OLIMEX/AgonLight2/HARDWARE/AgonLight2_Rev_B/3d/TFC-WPAPR-08---112J-TXAR-R_C_1-1.STEP

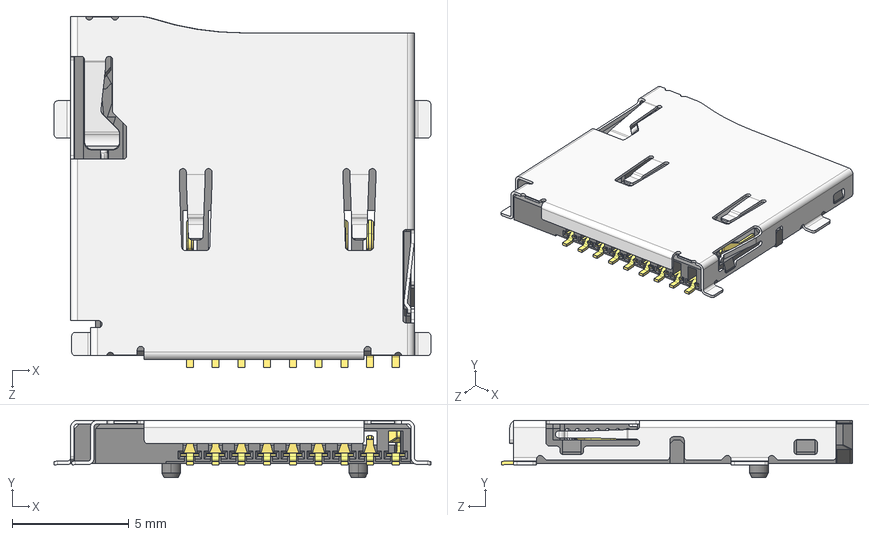
[picture p16: CAD file, 2023-07-12]
HARDWARE/AgonLight2_Rev_B/3d/TFC-WPAPR-08---112J-TXAR-R_C_1-1.STEP
16.1 x 2.45 x 15.0 mm
