OLIMEX/AgonLight2/HARDWARE/AgonLight2_Rev_B/3d/L-CD32_shielded.step

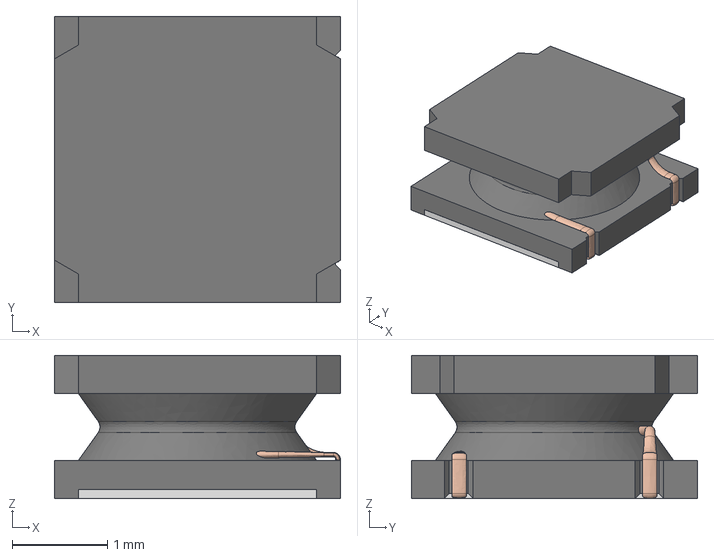
[picture p17: CAD file, 2023-07-12]
HARDWARE/AgonLight2_Rev_B/3d/L-CD32_shielded.step
3.00 x 3.00 x 1.50 mm
