OLIMEX/AgonLight2/HARDWARE/AgonLight2_Rev_B/3d/72w2538_292303-4.stp

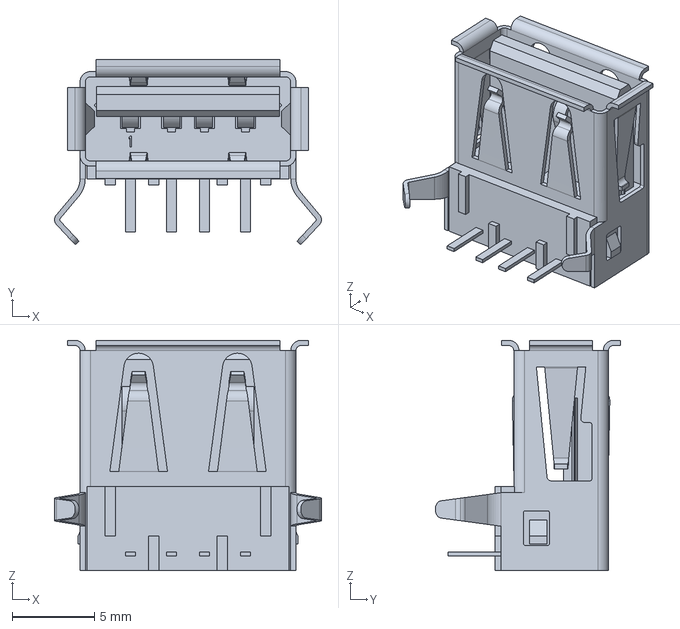
[picture p18: CAD file, 2023-07-12]
HARDWARE/AgonLight2_Rev_B/3d/72w2538_292303-4.stp
16.2 x 11.3 x 14.0 mm
