OLIMEX/AgonLight2/HARDWARE/AgonLight2_Rev_B/3d/DO-214AC_SMA.step

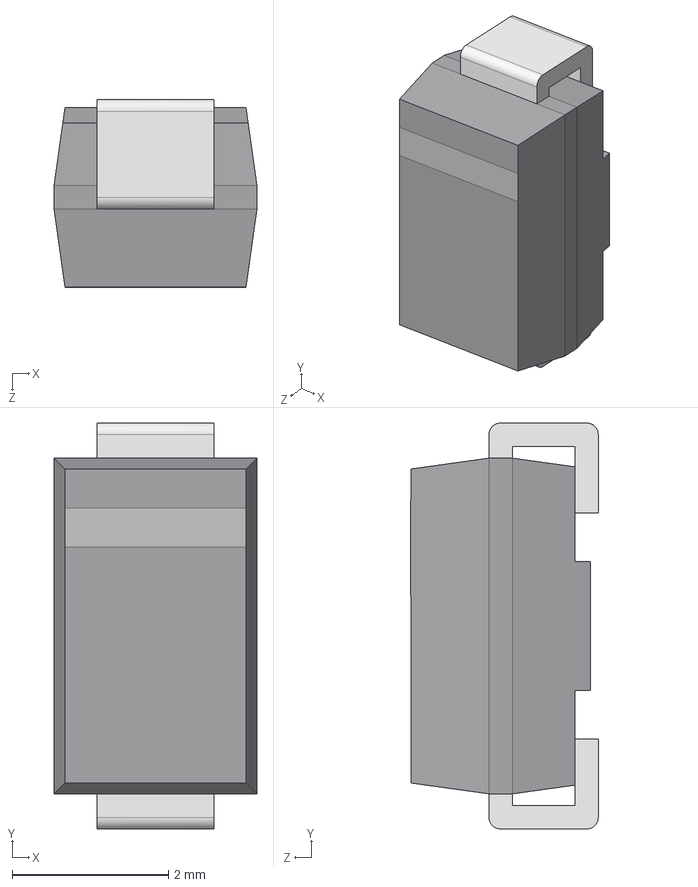
[picture p19: CAD file, 2023-07-12]
HARDWARE/AgonLight2_Rev_B/3d/DO-214AC_SMA.step
2.60 x 5.20 x 2.40 mm
