OLIMEX/AgonLight2/HARDWARE/AgonLight2_Rev_B/3d/Audio_Jack-3.5mm---CUI_SJ1-3515-SMT-TR.step

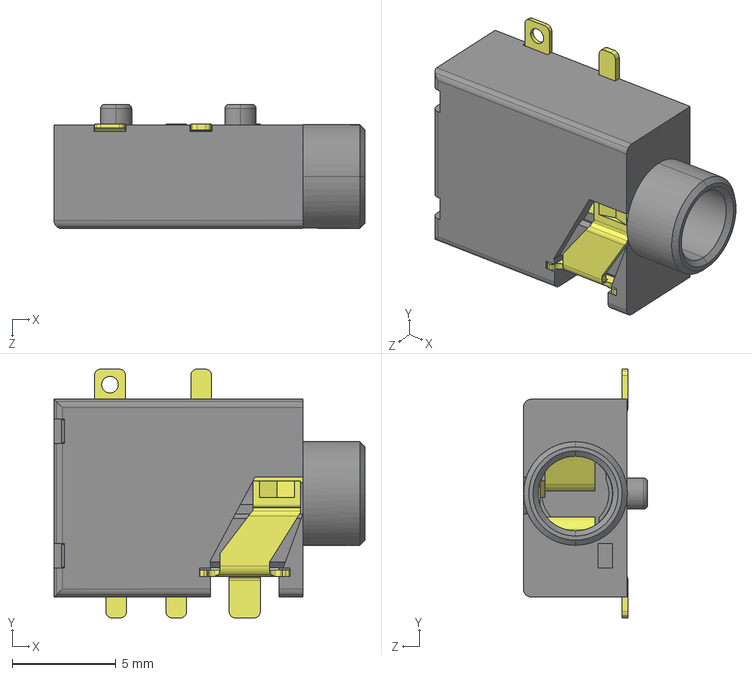
[picture p20: CAD file, 2023-07-12]
HARDWARE/AgonLight2_Rev_B/3d/Audio_Jack-3.5mm---CUI_SJ1-3515-SMT-TR.step
15.0 x 12.0 x 6.00 mm
