OLIMEX/AgonLight2/HARDWARE/AgonLight2_Rev_B/3d/JST_B2B-PH-SM4-TB(DW02R).step

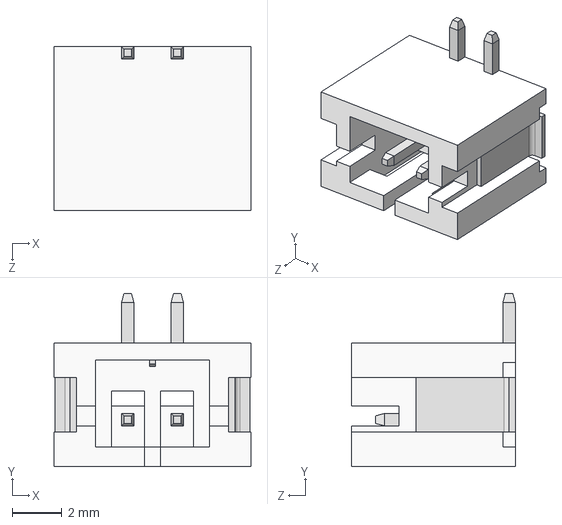
[picture p21: CAD file, 2023-07-12]
HARDWARE/AgonLight2_Rev_B/3d/JST_B2B-PH-SM4-TB(DW02R).step
7.95 x 7.00 x 6.60 mm
