OLIMEX/AgonLight2/HARDWARE/AgonLight2_Rev_B/3d/User Library-SOT50P160X60-6.step

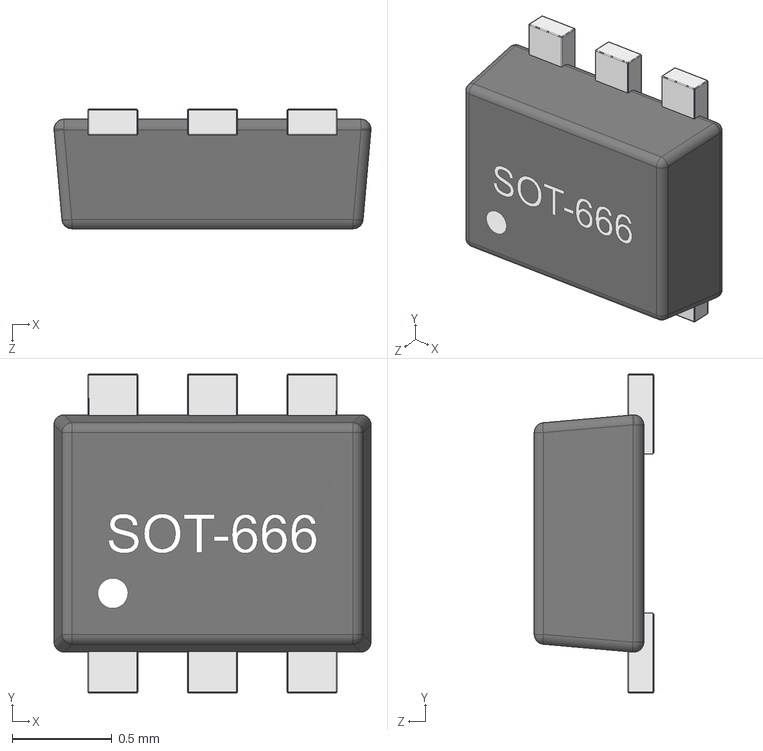
[picture p22: CAD file, 2023-07-12]
HARDWARE/AgonLight2_Rev_B/3d/User Library-SOT50P160X60-6.step
1.59 x 1.60 x 0.6 mm
