OLIMEX/AgonLight2/HARDWARE/AgonLight2_Rev_B/3d/SOT-23-6.step

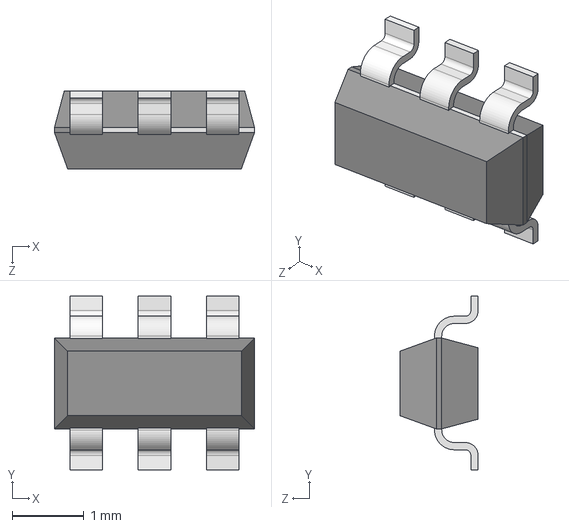
[picture p23: CAD file, 2023-07-12]
HARDWARE/AgonLight2_Rev_B/3d/SOT-23-6.step
2.79 x 2.43 x 1.09 mm
