OLIMEX/AgonLight2/HARDWARE/AgonLight2_Rev_B/3d/HN1x4-PinHeader_1x04_P2.54mm_Vertical.step

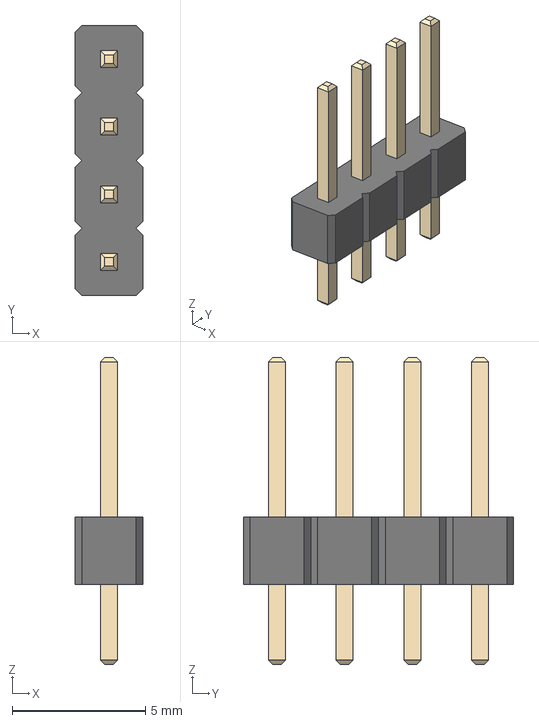
[picture p24: CAD file, 2022-12-14]
HARDWARE/AgonLight2_Rev_B/3d/HN1x4-PinHeader_1x04_P2.54mm_Vertical.step
2.54 x 10.2 x 11.5 mm
