OLIMEX/AgonLight2/HARDWARE/AgonLight2_Rev_B/3d/HN1x2-PinHeader_1x02_P2.54mm_Vertical.step

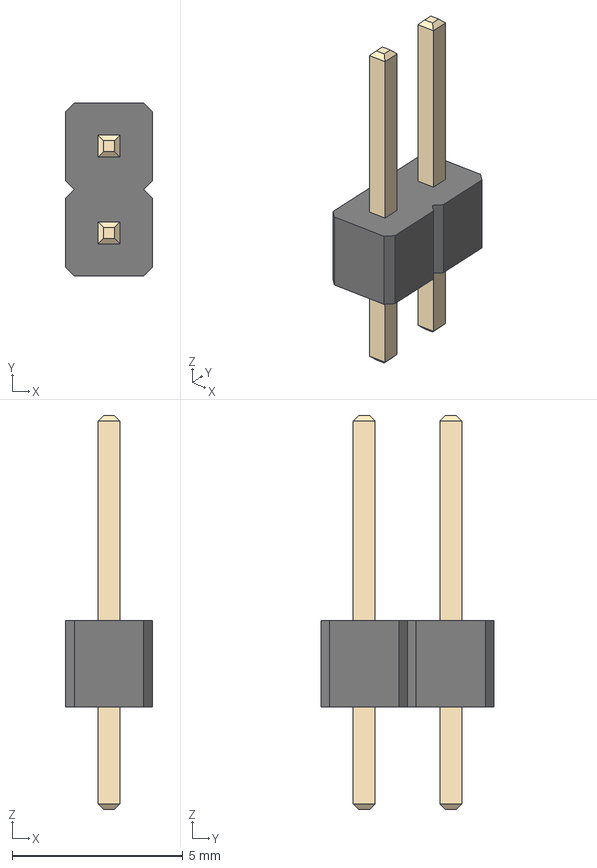
[picture p25: CAD file, 2022-12-14]
HARDWARE/AgonLight2_Rev_B/3d/HN1x2-PinHeader_1x02_P2.54mm_Vertical.step
2.54 x 5.08 x 11.5 mm
