OLIMEX/AgonLight2/SOFTWARE/4-AgonLight2-Console8/basic_examples_tests/olimex_challenge/ISSUE-3/SOLUTION-6/snakedemake.png

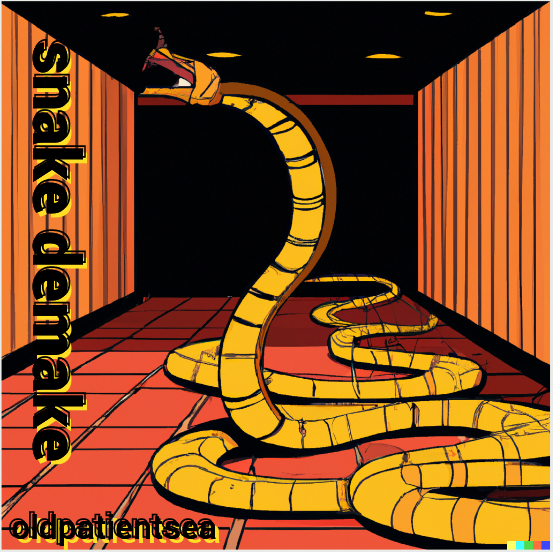
SOFTWARE/4-AgonLight2-Console8/basic_examples_tests/olimex_challenge/ISSUE-3/SOLUTION-6/snakedemake.png
