OLIMEX/AgonLight2/SOFTWARE/2-AgonLight2-VDP-104/source/video/agon_fonts.h

//
// Title:			Agon Video BIOS - font file
// Author:			Damien Guard
//					Lennart Benschop
// Created:			06/08/2022
// Last Updated:	20/02/2023
//
// Modinfo:
// 17/08/2022:		Implemented Acorn font
// 05/09/2022:		Renamed file
// 20/02/2023:		Marked out non-standard CP-1252 characters in comments, fixed £ and `
// 14/10/2023:		LB: Added CP1252 characters from BBC Basic for SDL2, kept all Agon ASCII characters as is, including £
//
// BBC Basic for SDL2 is
// Copyright (c) 2021, Richard T. Russell, http://www.rtrussell.co.uk/
// 
// This software is provided 'as-is', without any express or implied
// warranty.  In no event will the authors be held liable for any damages
// arising from the use of this software.

// Permission is granted to anyone to use this software for any purpose,
// including commercial applications, and to alter it and redistribute it
// freely, subject to the following restrictions:

// 1. The origin of this software must not be misrepresented; you must not
//    claim that you wrote the original software.  If you use this software
//    in a product, an acknowledgment in the product documentation would be
//    appreciated but is not required.

// 2. Altered source versions must be plainly marked as such, and must not be
//    misrepresented as being the original software.

// 3. This notice may not be removed or altered from any source distribution.

#pragma once

namespace fabgl {

	uint8_t FONT_AGON_DATA[256*8]; 

	static const uint8_t FONT_AGON_BITMAP[] = {
		0x00, 0x00, 0x00, 0x00, 0x00, 0x00, 0x00, 0x00, //  
		0x18, 0x18, 0x18, 0x18, 0x18, 0x00, 0x18, 0x00, // !
		0x6c, 0x6c, 0x6c, 0x00, 0x00, 0x00, 0x00, 0x00, // "
		0x36, 0x36, 0x7f, 0x36, 0x7f, 0x36, 0x36, 0x00, // #
		0x0c, 0x3f, 0x68, 0x3e, 0x0b, 0x7e, 0x18, 0x00, // $
		0x60, 0x66, 0x0c, 0x18, 0x30, 0x66, 0x06, 0x00, // %
		0x38, 0x6c, 0x6c, 0x38, 0x6d, 0x66, 0x3b, 0x00, // &
		0x0c, 0x18, 0x30, 0x00, 0x00, 0x00, 0x00, 0x00, // '
		0x0c, 0x18, 0x30, 0x30, 0x30, 0x18, 0x0c, 0x00, // (
		0x30, 0x18, 0x0c, 0x0c, 0x0c, 0x18, 0x30, 0x00, // )
		0x00, 0x18, 0x7e, 0x3c, 0x7e, 0x18, 0x00, 0x00, // *
		0x00, 0x18, 0x18, 0x7e, 0x18, 0x18, 0x00, 0x00, // +
		0x00, 0x00, 0x00, 0x00, 0x00, 0x18, 0x18, 0x30, // ,
		0x00, 0x00, 0x00, 0x7e, 0x00, 0x00, 0x00, 0x00, // -
		0x00, 0x00, 0x00, 0x00, 0x00, 0x18, 0x18, 0x00, // .
		0x00, 0x06, 0x0c, 0x18, 0x30, 0x60, 0x00, 0x00, // /

		0x3c, 0x66, 0x6e, 0x7e, 0x76, 0x66, 0x3c, 0x00, // 0
		0x18, 0x38, 0x18, 0x18, 0x18, 0x18, 0x7e, 0x00, // 1
		0x3c, 0x66, 0x06, 0x0c, 0x18, 0x30, 0x7e, 0x00, // 2
		0x3c, 0x66, 0x06, 0x1c, 0x06, 0x66, 0x3c, 0x00, // 3
		0x0c, 0x1c, 0x3c, 0x6c, 0x7e, 0x0c, 0x0c, 0x00, // 4
		0x7e, 0x60, 0x7c, 0x06, 0x06, 0x66, 0x3c, 0x00, // 5
		0x1c, 0x30, 0x60, 0x7c, 0x66, 0x66, 0x3c, 0x00, // 6
		0x7e, 0x06, 0x0c, 0x18, 0x30, 0x30, 0x30, 0x00, // 7
		0x3c, 0x66, 0x66, 0x3c, 0x66, 0x66, 0x3c, 0x00, // 8
		0x3c, 0x66, 0x66, 0x3e, 0x06, 0x0c, 0x38, 0x00, // 9
		0x00, 0x00, 0x18, 0x18, 0x00, 0x18, 0x18, 0x00, // :
		0x00, 0x00, 0x18, 0x18, 0x00, 0x18, 0x18, 0x30, // ;
		0x0c, 0x18, 0x30, 0x60, 0x30, 0x18, 0x0c, 0x00, // <
		0x00, 0x00, 0x7e, 0x00, 0x7e, 0x00, 0x00, 0x00, // =
		0x30, 0x18, 0x0c, 0x06, 0x0c, 0x18, 0x30, 0x00, // >
		0x3c, 0x66, 0x0c, 0x18, 0x18, 0x00, 0x18, 0x00, // ?

		0x3c, 0x66, 0x6e, 0x6a, 0x6e, 0x60, 0x3c, 0x00, // @
		0x3c, 0x66, 0x66, 0x7e, 0x66, 0x66, 0x66, 0x00, // A
		0x7c, 0x66, 0x66, 0x7c, 0x66, 0x66, 0x7c, 0x00, // B
		0x3c, 0x66, 0x60, 0x60, 0x60, 0x66, 0x3c, 0x00, // C
		0x78, 0x6c, 0x66, 0x66, 0x66, 0x6c, 0x78, 0x00, // D
		0x7e, 0x60, 0x60, 0x7c, 0x60, 0x60, 0x7e, 0x00, // E
		0x7e, 0x60, 0x60, 0x7c, 0x60, 0x60, 0x60, 0x00, // F
		0x3c, 0x66, 0x60, 0x6e, 0x66, 0x66, 0x3c, 0x00, // G
		0x66, 0x66, 0x66, 0x7e, 0x66, 0x66, 0x66, 0x00, // H
		0x7e, 0x18, 0x18, 0x18, 0x18, 0x18, 0x7e, 0x00, // I
		0x3e, 0x0c, 0x0c, 0x0c, 0x0c, 0x6c, 0x38, 0x00, // J
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
	};

	extern const FontInfo FONT_AGON = {
		.pointSize = 6,
		.width     = 8,
		.height    = 8,
		.ascent    = 7,
		.inleading = 0,
		.exleading = 0,
		.flags     = 0,
		.weight    = 400,
		.charset   = 255,
		.data      = FONT_AGON_DATA,
		.chptr     = nullptr,
		.codepage  = 1252,
	};
}
