OLIMEX/AgonLight2/SOFTWARE/2-AgonLight2-VDP-104/source/video/graphics.h

#ifndef GRAPHICS_H
#define GRAPHICS_H

#include <fabgl.h>

#include "agon.h"
#include "agon_ps2.h"
#include "agon_screen.h"
#include "agon_fonts.h"							// The Acorn BBC Micro Font
#include "agon_palette.h"						// Colour lookup table
#include "cursor.h"
#include "sprites.h"
#include "viewport.h"

fabgl::PaintOptions			gpo;				// Graphics paint options
fabgl::PaintOptions			tpo;				// Text paint options

Point			p1, p2, p3;						// Coordinate store for plot
Point			rp1, rp2, rp3;					// Relative coordinates store for plot
RGB888			gfg, gbg;						// Graphics foreground and background colour
RGB888			tfg, tbg;						// Text foreground and background colour
uint8_t			fontW;							// Font width
uint8_t			fontH;							// Font height
uint8_t			videoMode;						// Current video mode
bool			legacyModes = false;			// Default legacy modes being false
bool			rectangularPixels = false;		// Pixels are square by default
uint8_t			palette[64];					// Storage for the palette


// Copy the AGON font data from Flash to RAM
//
void copy_font() {
	memcpy(fabgl::FONT_AGON_DATA + 256, fabgl::FONT_AGON_BITMAP, sizeof(fabgl::FONT_AGON_BITMAP));
}

// Redefine a character in the font
//
void redefineCharacter(uint8_t c, uint8_t * data) {
	memcpy(&fabgl::FONT_AGON_DATA[c * 8], data, 8);
}

bool cmpChar(uint8_t * c1, uint8_t *c2, uint8_t len) {
	for (uint8_t i = 0; i < len; i++) {
		if (*c1++ != *c2++) {
			return false;
		}
	}
	return true;
}

// Try and match a character at given pixel position
//
char getScreenChar(uint16_t px, uint16_t py) {
	RGB888	pixel;
	uint8_t	charRow;
	uint8_t	charData[8];
	uint8_t R = tbg.R;
	uint8_t G = tbg.G;
	uint8_t B = tbg.B;

	// Do some bounds checking first
	//
	if (px >= canvasW - 8 || py >= canvasH - 8) {
		return 0;
	}
	if (ttxtMode) {
		return ttxt_instance.get_screen_char(px,py);
	} else {
		// Now scan the screen and get the 8 byte pixel representation in charData
		//
		for (uint8_t y = 0; y < 8; y++) {
	    	charRow = 0;
	    	for (uint8_t x = 0; x < 8; x++) {
	      		pixel = canvas->getPixel(px + x, py + y);
	      		if (!(pixel.R == R && pixel.G == G && pixel.B == B)) {
					charRow |= (0x80 >> x);
	    		}
	    	}
	    	charData[y] = charRow;
		}
		//
		// Finally try and match with the character set array
		//
		for (auto i = 32; i <= 255; i++) {
	    	if (cmpChar(charData, &fabgl::FONT_AGON_DATA[i * 8], 8)) {	
	    		return i;		
			}
		}
	}
	return 0;
}

// Get pixel value at screen coordinates
//
RGB888 getPixel(uint16_t x, uint16_t y) {
	Point p = translateCanvas(scale(x, y));
	if (p.X >= 0 && p.Y >= 0 && p.X < canvasW && p.Y < canvasH) {
		return canvas->getPixel(p.X, p.Y);
	}
	return RGB888(0,0,0);
}

// Get the palette index for a given RGB888 colour
//
uint8_t getPaletteIndex(RGB888 colour) {
	for (uint8_t i = 0; i < getVGAColourDepth(); i++) {
		if (colourLookup[palette[i]] == colour) {
			return i;
		}
	}
	return 0;
}

// Set logical palette
// Parameters:
// - l: The logical colour to change
// - p: The physical colour to change
// - r: The red component
// - g: The green component
// - b: The blue component
//
void setPalette(uint8_t l, uint8_t p, uint8_t r, uint8_t g, uint8_t b) {
	RGB888 col;				// The colour to set

	if (getVGAColourDepth() < 64) {		// If it is a paletted video mode
		if (p == 255) {					// If p = 255, then use the RGB values
			col = RGB888(r, g, b);
		} else if (p < 64) {			// If p < 64, then look the value up in the colour lookup table
			col = colourLookup[p];
		} else {				
			debug_log("vdu_palette: p=%d not supported\n\r", p);
			return;
		}
		setPaletteItem(l, col);
		debug_log("vdu_palette: %d,%d,%d,%d,%d\n\r", l, p, r, g, b);
	} else {
		debug_log("vdu_palette: not supported in this mode\n\r");
	}
}

// Reset the palette and set the foreground and background drawing colours
// Parameters:
// - colour: Array of indexes into colourLookup table
// - sizeOfArray: Size of passed colours array
//
void resetPalette(const uint8_t colours[]) {
	if (ttxtMode) return;
	for (uint8_t i = 0; i < 64; i++) {
		uint8_t c = colours[i % getVGAColourDepth()];
		palette[i] = c;
		setPaletteItem(i, colourLookup[c]);
	}
	updateRGB2PaletteLUT();
}

// Get the paint options for a given GCOL mode
//
fabgl::PaintOptions getPaintOptions(uint8_t mode, fabgl::PaintOptions priorPaintOptions) {
	fabgl::PaintOptions p = priorPaintOptions;
	
	switch (mode) {
		case 0: p.NOT = 0; p.swapFGBG = 0; break;
		case 4: p.NOT = 1; p.swapFGBG = 0; break;
	}
	return p;
}

// Set text colour (handles COLOUR / VDU 17)
//
void setTextColour(uint8_t colour) {
	if (ttxtMode) return;

	uint8_t c = palette[colour % getVGAColourDepth()];

	if (colour < 64) {
		tfg = colourLookup[c];
		debug_log("vdu_colour: tfg %d = %02X : %02X,%02X,%02X\n\r", colour, c, tfg.R, tfg.G, tfg.B);
	}
	else if (colour >= 128 && colour < 192) {
		tbg = colourLookup[c];
		debug_log("vdu_colour: tbg %d = %02X : %02X,%02X,%02X\n\r", colour, c, tbg.R, tbg.G, tbg.B);	
	}
	else {
		debug_log("vdu_colour: invalid colour %d\n\r", colour);
	}
}

// Set graphics colour (handles GCOL / VDU 18)
//
void setGraphicsColour(uint8_t mode, uint8_t colour) {
	if (ttxtMode) return;
	
	uint8_t c = palette[colour % getVGAColourDepth()];

	if (mode <= 6) {
		if (colour < 64) {
			gfg = colourLookup[c];
			debug_log("vdu_gcol: mode %d, gfg %d = %02X : %02X,%02X,%02X\n\r", mode, colour, c, gfg.R, gfg.G, gfg.B);
		}
		else if (colour >= 128 && colour < 192) {
			gbg = colourLookup[c];
			debug_log("vdu_gcol: mode %d, gbg %d = %02X : %02X,%02X,%02X\n\r", mode, colour, c, gbg.R, gbg.G, gbg.B);
		}
		else {
			debug_log("vdu_gcol: invalid colour %d\n\r", colour);
		}
		gpo = getPaintOptions(mode, gpo);
	}
	else {
		debug_log("vdu_gcol: invalid mode %d\n\r", mode);
	}
}

// Clear a viewport
//
void clearViewport(Rect * viewport) {
	if (ttxtMode) {
		ttxt_instance.cls();
	} else {       
  		if (canvas) {
	  		if (useViewports) {
		  		canvas->fillRectangle(*viewport);
		  	}
		  	else {
			  canvas->clear();
			}
	  	}
	}
}

//// Graphics drawing routines

// Push point to list
//
void pushPoint(Point p) {
	rp3 = rp2;
	rp2 = rp1;
	rp1 = Point(p.X - p1.X, p.Y - p1.Y);
	p3 = p2;
	p2 = p1;
	p1 = p;
}
void pushPoint(uint16_t x, uint16_t y) {
	pushPoint(translateCanvas(scale(x, y)));
}
void pushPointRelative(int16_t x, int16_t y) {
	auto scaledPoint = scale(x, y);
	pushPoint(Point(p1.X + scaledPoint.X, p1.Y + (logicalCoords ? -scaledPoint.Y : scaledPoint.Y)));
}

// get graphics cursor
//
Point * getGraphicsCursor() {
	return &p1;
}

// Set up canvas for drawing graphics
//
void setGraphicsOptions(uint8_t mode) {
	auto colourMode = mode & 0x03;
	canvas->setClippingRect(graphicsViewport);
	switch (colourMode) {
		case 0: break;	// move command
		case 1: {
			// use fg colour
			canvas->setPenColor(gfg);
		} break;
		case 2: break;	// logical inverse colour (not suported)
		case 3: {
			// use bg colour
			canvas->setPenColor(gbg);
		} break;
	}
	canvas->setPaintOptions(gpo);
}

// Set up canvas for drawing filled graphics
//
void setGraphicsFill(uint8_t mode) {
	auto colourMode = mode & 0x03;
	switch (colourMode) {
		case 0: break;	// move command
		case 1: {
			// use fg colour
			canvas->setBrushColor(gfg);
		} break;
		case 2: break;	// logical inverse colour (not suported)
		case 3: {
			// use bg colour
			canvas->setBrushColor(gbg);
		} break;
	}
}

// Move to
//
void moveTo() {
	canvas->moveTo(p1.X, p1.Y);
}

// Line plot
//
void plotLine(bool omitFirstPoint = false, bool omitLastPoint = false) {
	RGB888 firstPixelColour;
	RGB888 lastPixelColour;
	if (omitFirstPoint) {
		firstPixelColour = canvas->getPixel(p2.X, p2.Y);
	}
	if (omitLastPoint) {
		lastPixelColour = canvas->getPixel(p1.X, p1.Y);
	}
	canvas->lineTo(p1.X, p1.Y);
	if (omitFirstPoint) {
		canvas->setPixel(p2, firstPixelColour);
	}
	if (omitLastPoint) {
		canvas->setPixel(p1, lastPixelColour);
	}
}

// Point point
//
void plotPoint() {
	canvas->setPixel(p1.X, p1.Y);
}

// Triangle plot
//
void plotTriangle() {
	Point p[3] = {
		p3,
		p2,
		p1, 
	};
	canvas->drawPath(p, 3);
	canvas->fillPath(p, 3);
}

// Rectangle plot
//
void plotRectangle() {
	canvas->fillRectangle(p2.X, p2.Y, p1.X, p1.Y);
}

// Parallelogram plot
//
void plotParallelogram() {
	Point p[4] = {
		p3,
		p2,
		p1,
		Point(p1.X + (p3.X - p2.X), p1.Y + (p3.Y - p2.Y)),
	};
	canvas->drawPath(p, 4);
	canvas->fillPath(p, 4);
}

// Circle plot
//
void plotCircle(bool filled = false) {
	auto size = 2 * sqrt(rp1.X * rp1.X + (rp1.Y * rp1.Y * (rectangularPixels ? 4 : 1)));
	if (filled) {
		canvas->fillEllipse(p2.X, p2.Y, size, rectangularPixels ? size / 2 : size);
	} else {
		canvas->drawEllipse(p2.X, p2.Y, size, rectangularPixels ? size / 2 : size);
	}
}

// Copy or move a rectangle
//
void plotCopyMove(uint8_t mode) {
	uint16_t x = p1.X;
	uint16_t y = p1.Y;
	uint16_t width = abs(p3.X - p2.X) + 1;
	uint16_t height = abs(p3.Y - p2.Y) + 1;
	uint16_t sourceX = p3.X < p2.X ? p3.X : p2.X;
	uint16_t sourceY = p3.Y < p2.Y ? p3.Y : p2.Y;

	debug_log("plotCopyMove: mode %d, (%d,%d) -> (%d,%d), width: %d, height: %d\n\r", mode, sourceX, sourceY, x, y, width, height);
	canvas->copyRect(sourceX, sourceY, x, y - height, width, height);
	if (mode == 1 || mode == 5) {
		// move rectangle needs to clear source rectangle
		// being careful not to clear the destination rectangle
		canvas->setBrushColor(gbg);
		Rect sourceRect = Rect(sourceX, sourceY, sourceX + width, sourceY + height);
		Rect destRect = Rect(x, y - height, x + width, y);
		if (sourceRect.intersects(destRect)) {
			// we can use clipping rects to block out parts of the screen
			// the areas above, below, left, and right of the destination rectangle
			// and then draw rectangles over our source rectangle
			auto intersection = sourceRect.intersection(destRect);

			if (intersection.X1 > sourceRect.X1) {
				// fill in source area to the left of destination
				debug_log("clearing left of destination\n\r");
				canvas->setClippingRect(Rect(sourceRect.X1, sourceRect.Y1, intersection.X1 - 1, sourceRect.Y2));
				canvas->fillRectangle(sourceRect);
			}
			if (intersection.X2 < sourceRect.X2) {
				// fill in source area to the right of destination
				debug_log("clearing right of destination\n\r");
				canvas->setClippingRect(Rect(intersection.X2, sourceRect.Y1, sourceRect.X2, sourceRect.Y2));
				canvas->fillRectangle(sourceRect);
			}
			if (intersection.Y1 > sourceRect.Y1) {
				// fill in source area above destination
				debug_log("clearing above destination\n\r");
				canvas->setClippingRect(Rect(sourceRect.X1, sourceRect.Y1, sourceRect.X2, intersection.Y1 - 1));
				canvas->fillRectangle(sourceRect);
			}
			if (intersection.Y2 < sourceRect.Y2) {
				// fill in source area below destination
				debug_log("clearing below destination\n\r");
				canvas->setClippingRect(Rect(sourceRect.X1, intersection.Y2, sourceRect.X2, sourceRect.Y2));
				canvas->fillRectangle(sourceRect);
			}
		} else {
			canvas->fillRectangle(sourceRect);
		}
	}
}

// Plot bitmap
//
void plotBitmap() {
	drawBitmap(p1.X, p1.Y);
}

// Character plot
//
void plotCharacter(char c) {
	if (ttxtMode) {
    	ttxt_instance.draw_char(activeCursor->X, activeCursor->Y, c);
  	} else {
  		if (textCursorActive()) {
	  		canvas->setClippingRect(defaultViewport);
			canvas->setPenColor(tfg);
			canvas->setBrushColor(tbg);
			canvas->setPaintOptions(tpo);
	  	} else {
		  canvas->setClippingRect(graphicsViewport);
		  canvas->setPenColor(gfg);
		  canvas->setPaintOptions(gpo);
		}
		canvas->drawChar(activeCursor->X, activeCursor->Y, c);
  	}
	cursorRight();
}

// Backspace plot
//
void plotBackspace() {
	cursorLeft();
	if (ttxtMode) {
		ttxt_instance.draw_char(activeCursor->X, activeCursor->Y, ' ');
	} else {
		canvas->setBrushColor(textCursorActive() ? tbg : gbg);
		canvas->fillRectangle(activeCursor->X, activeCursor->Y, activeCursor->X + fontW - 1, activeCursor->Y + fontH - 1);
	}
}

// Set character overwrite mode (background fill)
//
inline void setCharacterOverwrite(bool overwrite) {
	canvas->setGlyphOptions(GlyphOptions().FillBackground(overwrite));
}

// Set a clipping rectangle
//
void setClippingRect(Rect rect) {
	canvas->setClippingRect(rect);
}

// Draw cursor
//
void drawCursor(Point p) {
	canvas->swapRectangle(p.X, p.Y, p.X + fontW - 1, p.Y + fontH - 1);
}


// Clear the screen
// 
void cls(bool resetViewports) {
	if (resetViewports) {
    	if (ttxtMode) {
    		ttxt_instance.set_window(0,24,39,0);
		}
		viewportReset();
	}
	if (canvas) {
		canvas->setPenColor(tfg);
		canvas->setBrushColor(tbg);	
		canvas->setPaintOptions(tpo);
		clearViewport(getViewport(VIEWPORT_TEXT));
	}
	if (hasActiveSprites()) {
		activateSprites(0);
		clearViewport(getViewport(VIEWPORT_TEXT));
	}
	homeCursor();
	setPagedMode();
}

// Clear the graphics area
//
void clg() {
	if (canvas) {
		canvas->setPenColor(gfg);
		canvas->setBrushColor(gbg);	
		canvas->setPaintOptions(gpo);
		clearViewport(getViewport(VIEWPORT_GRAPHICS));
	}
	pushPoint(0, 0);		// Reset graphics origin (as per BBC Micro CLG)
}

// Do the mode change
// Parameters:
// - mode: The video mode
// Returns:
// -  0: Successful
// -  1: Invalid # of colours
// -  2: Not enough memory for mode
// - -1: Invalid mode
//
int8_t change_mode(uint8_t mode) {
	int8_t errVal = -1;

	cls(true);
	ttxtMode = false;
	switch (mode) {
		case 0:
			if (legacyModes == true) {
				errVal = change_resolution(2, SVGA_1024x768_60Hz);
			} else {
				errVal = change_resolution(16, VGA_640x480_60Hz);	// VDP 1.03 Mode 3, VGA Mode 12h
			}
			break;
		case 1:
			if (legacyModes == true) {
				errVal = change_resolution(16, VGA_512x384_60Hz);
			} else {
				errVal = change_resolution(4, VGA_640x480_60Hz);
			}
			break;
		case 2:
			if (legacyModes == true) {
				errVal = change_resolution(64, VGA_320x200_75Hz);
			} else {
				errVal = change_resolution(2, VGA_640x480_60Hz);
			}
			break;
		case 3:
			if (legacyModes == true) {
				errVal = change_resolution(16, VGA_640x480_60Hz);
			} else {
				errVal = change_resolution(64, VGA_640x240_60Hz);
			}
			break;
		case 4:
			errVal = change_resolution(16, VGA_640x240_60Hz);
			break;
		case 5:
			errVal = change_resolution(4, VGA_640x240_60Hz);
			break;
		case 6:
			errVal = change_resolution(2, VGA_640x240_60Hz);
			break;
		case 7:
	    	errVal = change_resolution(16, VGA_640x480_60Hz);
	    	if (errVal == 0) {
	      		errVal = ttxt_instance.init();
	    		if (errVal == 0) ttxtMode = true; 
	    	}
	    	break;
		case 8:
			errVal = change_resolution(64, QVGA_320x240_60Hz);		// VGA "Mode X"
			break;
		case 9:
			errVal = change_resolution(16, QVGA_320x240_60Hz);
			break;
		case 10:
			errVal = change_resolution(4, QVGA_320x240_60Hz);
			break;
		case 11:
			errVal = change_resolution(2, QVGA_320x240_60Hz);
			break;
		case 12:
			errVal = change_resolution(64, VGA_320x200_70Hz);		// VGA Mode 13h
			break;
		case 13:
			errVal = change_resolution(16, VGA_320x200_70Hz);
			break;
		case 14:
			errVal = change_resolution(4, VGA_320x200_70Hz);
			break;
		case 15:
			errVal = change_resolution(2, VGA_320x200_70Hz);
			break;
		case 16:
			errVal = change_resolution(4, SVGA_800x600_60Hz);
			break;
		case 17:
			errVal = change_resolution(2, SVGA_800x600_60Hz);
			break;
		case 18:
			errVal = change_resolution(2, SVGA_1024x768_60Hz);		// VDP 1.03 Mode 0
			break;
		case 129:
			errVal = change_resolution(4, VGA_640x480_60Hz, true);
			break;
		case 130:
			errVal = change_resolution(2, VGA_640x480_60Hz, true);
			break;
		case 132:
			errVal = change_resolution(16, VGA_640x240_60Hz, true);
			break;
		case 133:
			errVal = change_resolution(4, VGA_640x240_60Hz, true);
			break;
		case 134:
			errVal = change_resolution(2, VGA_640x240_60Hz, true);
			break;
		case 136:
			errVal = change_resolution(64, QVGA_320x240_60Hz, true);		// VGA "Mode X"
			break;
		case 137:
			errVal = change_resolution(16, QVGA_320x240_60Hz, true);
			break;
		case 138:
			errVal = change_resolution(4, QVGA_320x240_60Hz, true);
			break;	
		case 139:
			errVal = change_resolution(2, QVGA_320x240_60Hz, true);
			break;
		case 140:
			errVal = change_resolution(64, VGA_320x200_70Hz, true);		// VGA Mode 13h
			break;
		case 141:
			errVal = change_resolution(16, VGA_320x200_70Hz, true);
			break;
		case 142:
			errVal = change_resolution(4, VGA_320x200_70Hz, true);
			break;
		case 143:
			errVal = change_resolution(2, VGA_320x200_70Hz, true);
			break;									
	}
	if (errVal != 0) {
		return errVal;
	}
	switch (getVGAColourDepth()) {
		case  2: resetPalette(defaultPalette02); break;
		case  4: resetPalette(defaultPalette04); break;
		case  8: resetPalette(defaultPalette08); break;
		case 16: resetPalette(defaultPalette10); break;
		case 64: resetPalette(defaultPalette40); break;
	}
	tpo = getPaintOptions(0, tpo);
	gpo = getPaintOptions(0, gpo);
	gfg = colourLookup[0x3F];
	gbg = colourLookup[0x00];
	tfg = colourLookup[0x3F];
	tbg = colourLookup[0x00];
	if (!ttxtMode) {
		canvas->selectFont(&fabgl::FONT_AGON);
	}
	setCharacterOverwrite(true);
	canvas->setPenWidth(1);
	setCanvasWH(canvas->getWidth(), canvas->getHeight());
	// simple heuristic to determine rectangular pixels
	rectangularPixels = ((float)canvasW / (float)canvasH) > 2;
	fontW = canvas->getFontInfo()->width;
	fontH = canvas->getFontInfo()->height;
	viewportReset();
	setOrigin(0,0);
	pushPoint(0,0);
	pushPoint(0,0);
	pushPoint(0,0);
	moveTo();
	resetCursor();
	homeCursor();
	if (isDoubleBuffered()) {
		switchBuffer();
		cls(false);
	}
	resetMousePositioner(canvasW, canvasH, _VGAController.get());
	setMouseCursor();
	debug_log("do_modeChange: canvas(%d,%d), scale(%f,%f), mode %d, videoMode %d\n\r", canvasW, canvasH, logicalScaleX, logicalScaleY, mode, videoMode);
	return 0;
}

// Change the video mode
// If there is an error, restore the last mode
// Parameters:
// - mode: The video mode
//
void set_mode(uint8_t mode) {
	auto errVal = change_mode(mode);
	if (errVal != 0) {
		debug_log("set_mode: error %d\n\r", errVal);
		errVal = change_mode(videoMode);
		if (errVal != 0) {
			debug_log("set_mode: error %d on restoring mode\n\r", errVal);
			videoMode = 1;
			change_mode(1);
		}
		return;
	}
	videoMode = mode;
}

void setLegacyModes(bool legacy) {
	legacyModes = legacy;
}

void scrollRegion(Rect * region, uint8_t direction, int16_t movement) {
	canvas->setScrollingRegion(region->X1, region->Y1, region->X2, region->Y2);
	if (ttxtMode) {
    	if (direction == 3) ttxt_instance.scroll();
  	} else {
		switch (direction) {
			case 0:	// Right
				canvas->scroll(movement, 0);
		  		break;
			case 1: // Left
				canvas->scroll(-movement, 0);
				break;
			case 2: // Down
				canvas->scroll(0, movement);
				break;
			case 3: // Up
				canvas->scroll(0, -movement);
				break;
  		}
  	} 
}

#endif
