OLIMEX/AgonLight2/SOFTWARE/2-AgonLight2-VDP-104/source/video/ttxtfont.h

/*****************************************************************\
*   BBC BASIC for SDL 2.0 (32-bit Web Assembly)                   *
*   Copyright (c) R. T. Russell, 2000-2021                        *
*                                                                 *
*   BBDATA_WASM.C RAM data definitions                            *
*   Version 1.22a, 15-May-2021                                    *
\*****************************************************************/
// 06/05/2023 Extract just the teletext font from this file.

const unsigned short ttxtfont[256*20] = {
	0x0000,0x0011,0x0011,0x0019,0x0015,0x0013,0x0011,0x0011,0x8800,0x8800,0x8800,0x8800,0x8800,0x8800,0x7000,0x0000,0x0000,0x0000,0x0000,0x0000, // NU
	0x0000,0x000E,0x0011,0x0011,0x001F,0x0011,0x0011,0x0011,0xF000,0x8800,0x8800,0xF000,0x8800,0x8800,0x8800,0x0000,0x0000,0x0000,0x0000,0x0000, // AR
	0x0000,0x000E,0x0011,0x0011,0x001F,0x0011,0x0011,0x0011,0x7000,0x8800,0x8000,0x9800,0x8800,0x8800,0x7000,0x0000,0x0000,0x0000,0x0000,0x0000, // AG
	0x0000,0x000E,0x0011,0x0011,0x001F,0x0011,0x0011,0x0011,0x8800,0x8800,0x5000,0x2000,0x2000,0x2000,0x2000,0x0000,0x0000,0x0000,0x0000,0x0000, // AY
	0x0000,0x000E,0x0011,0x0011,0x001F,0x0011,0x0011,0x0011,0xF000,0x8800,0x8800,0xF000,0x8800,0x8800,0xF000,0x0000,0x0000,0x0000,0x0000,0x0000, // AB
	0x0000,0x000E,0x0011,0x0011,0x001F,0x0011,0x0011,0x0011,0x8800,0xD800,0xA800,0xA800,0x8800,0x8800,0x8800,0x0000,0x0000,0x0000,0x0000,0x0000, // AM
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
	0x0006,0x0007,0x8003,0x8001,0x0000,0xFC3F,0xFC3F,0x0030,0x0030,0xF03F,0xF03F,0x0030,0x0030,0xFC3F,0xFC3F,0x0000,0x0000,0x0000,0x0000,0x0000, // "È"
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
