OLIMEX/AgonLight2/SOFTWARE/3-AgonLight2-MOS-104/src/keyboard.asm

;
; Title:	AGON MOS - Keyboard routines
; Author:	Dean Belfield
; Created:	13/08/2023
; Last Updated:	13/08/2023
;
; Modinfo:
			INCLUDE	"macros.inc"
			INCLUDE	"equs.inc"

			.ASSUME	ADL = 1

			DEFINE .STARTUP, SPACE = ROM
			SEGMENT .STARTUP

			XDEF	keyboard_handler

			XREF	_keymods 			; In globals.asm
			XREF	_keyascii
			XREF	_keycode
			XREF	_keymap

; Agon keyboard routines
;  C: Keydown state (1 = pressed 0 = depressed)
;  B: Virtual keycode
;
keyboard_handler:	LD	A, B
			OR	A
			CALL	NZ, keyboard_map
			JP	keyboard_reset

; Write key up and down states to the keymap
;  C: Keydown state (1 = pressed 0 = depressed)
;  A: Virtual keycode
;
keyboard_map:		DEC	A 				;  A: Virtual keycode - 1
			LD	DE, keyboard_lookup		; DE: Address of keyboard lookup table
			LD	HL, 0
			LD	L, A 
			ADD	HL, HL 
			ADD	HL, HL				; HL: Virtual keycode x 4
			ADD	HL, DE				; HL: Address of key data in keyboard lookup
			LD	A, (HL)				;  A: Bit to set
			OR	A				; Check for empty entry
			RET	Z				; Yep, nothing to set here, so return
			INC	HL
			LD	HL, (HL)			; HL: Address to set into
			BIT 	0, C				; Is the key down or up?
			JR	NZ, $F 				; It is down so jump to the code that sets a bit
			CPL					; It is up so complement the bit
			AND	(HL)				; Then AND it with the keymap entry
			LD	(HL), A
			RET 
;
$$:			OR	(HL)				; OR with the keymap entry
			LD	(HL), A
			RET 
;			
; Now check for CTRL+ALT+DEL
;
keyboard_reset:		LD	A, B				; Get the virtual key code
			CP	130				; Check for DEL (cursor keys)
			JR	Z, $F
			CP	131				; Check for DEL (no numlock)
			JR	Z , $F
			CP	88				; And DEL (numlock)
			RET	NZ
$$:			LD	A, (_keymods)			; DEL is pressed so check CTRL + ALT
			AND	05h				; Bit 0 and 2
			CP	05h
			RET	NZ				; Exit if not pressed
;
; Here we're just waiting for the key to go up
;
			LD	A, C				; Get key down
			DEC	A				; Check for 0 (key up)
			JP	NZ, 0				; Yes so reset
			LD	(_keyascii), A			; Otherwise clear the keycode so no interaction with console 
			LD	(_keycode), A 
			RET
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
